Hajar2314/HawkEye-Rescue-Drone-Module/media/heatmap_0003.png

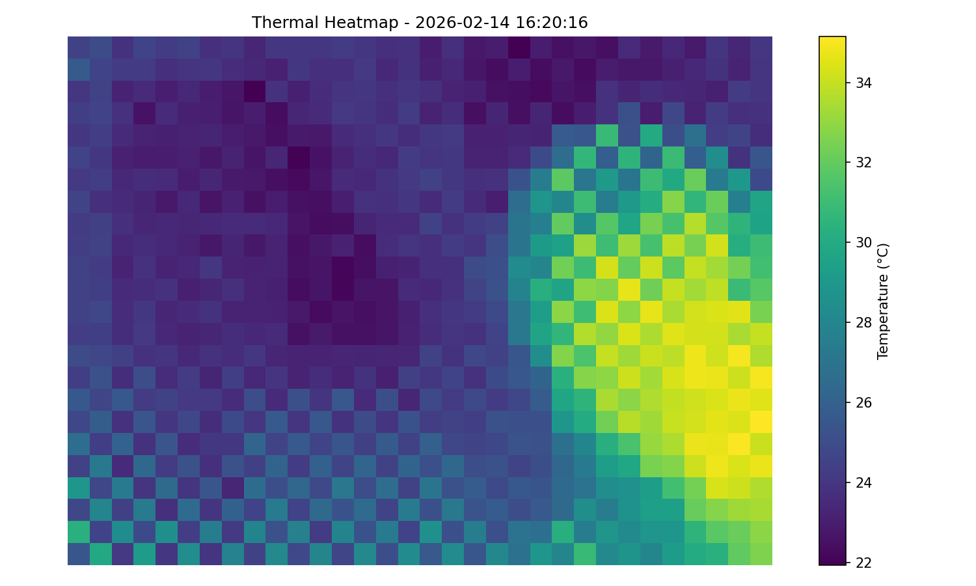
media/heatmap_0003.png
