Hajar2314/HawkEye-Rescue-Drone-Module/media/heatmap_images/heatmap_0002.png

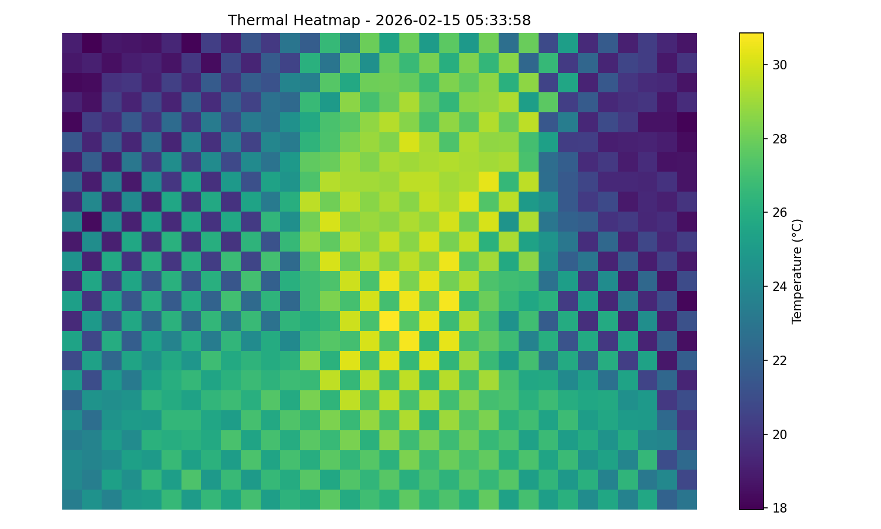
media/heatmap_images/heatmap_0002.png
