Hajar2314/HawkEye-Rescue-Drone-Module/media/heatmap_images/heatmap_0004.png

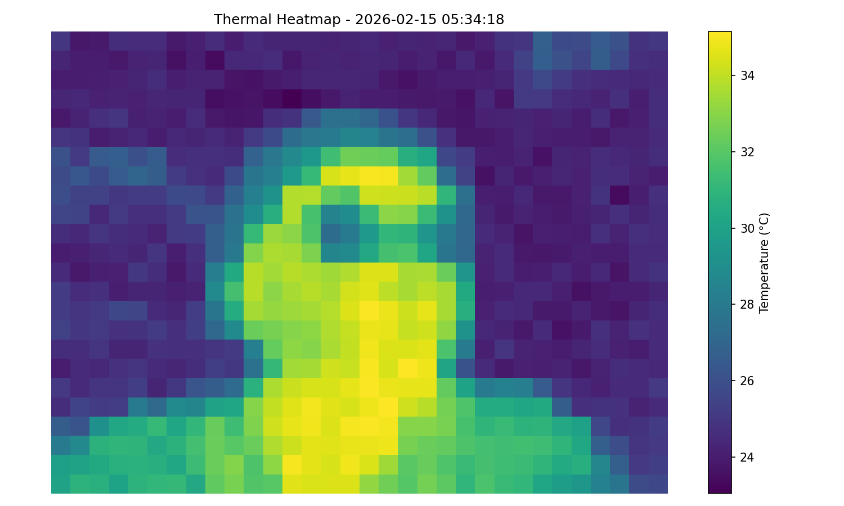
media/heatmap_images/heatmap_0004.png
