Hajar2314/HawkEye-Rescue-Drone-Module/media/heatmap_images/heatmap_0005.png

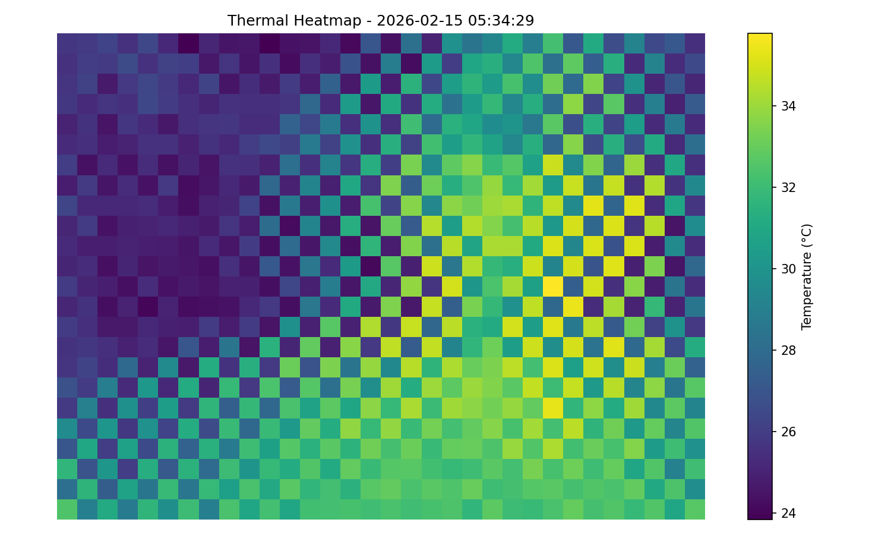
media/heatmap_images/heatmap_0005.png
