Hajar2314/HawkEye-Rescue-Drone-Module/media/photo_323210312788.jpg

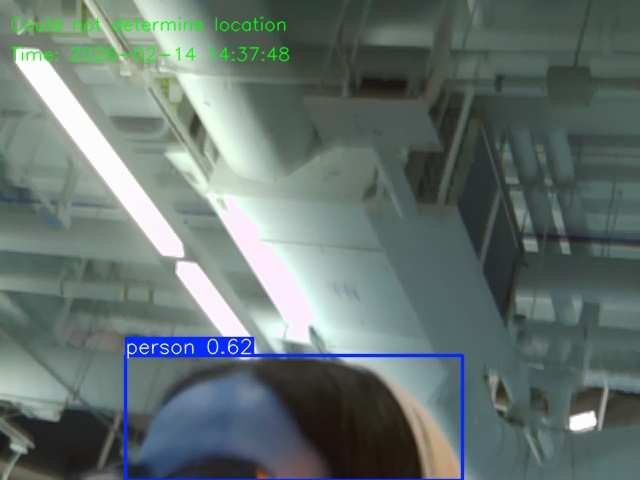
media/photo_323210312788.jpg
