Hajar2314/HawkEye-Rescue-Drone-Module/media/photo_6040880837786.jpg

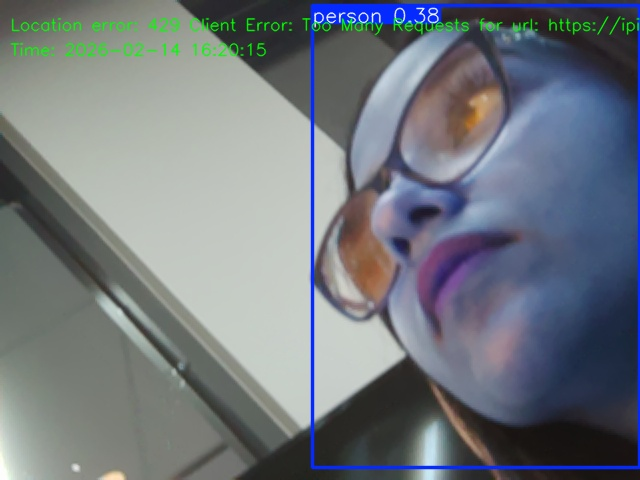
media/photo_6040880837786.jpg
