Hajar2314/HawkEye-Rescue-Drone-Module/media/Screenshot-dump/photo_65979483033.jpg

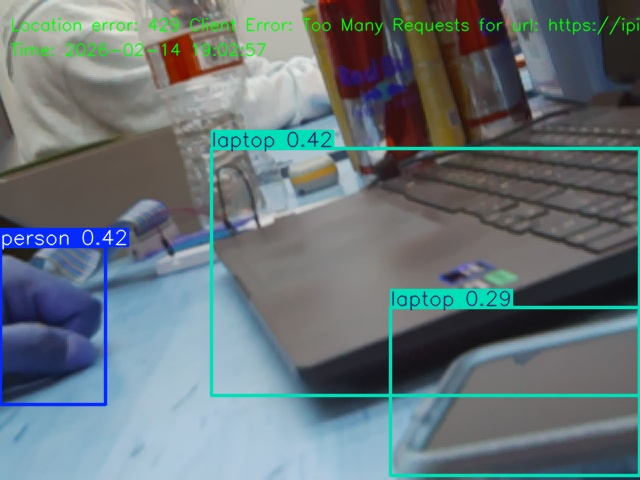
media/Screenshot-dump/photo_65979483033.jpg
