Hajar2314/HawkEye-Rescue-Drone-Module/media/Screenshot-dump/photo_150695907242.jpg

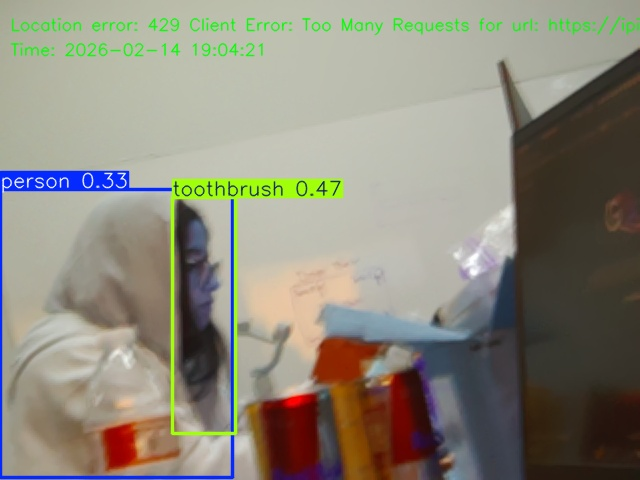
media/Screenshot-dump/photo_150695907242.jpg
