Hajar2314/HawkEye-Rescue-Drone-Module/media/Screenshot-dump/photo_160943007310.jpg

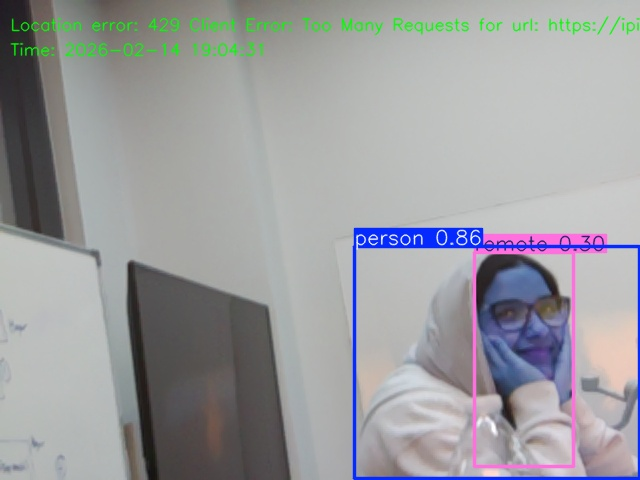
media/Screenshot-dump/photo_160943007310.jpg
