Hajar2314/HawkEye-Rescue-Drone-Module/media/Screenshot-dump/photo_250089213979.jpg

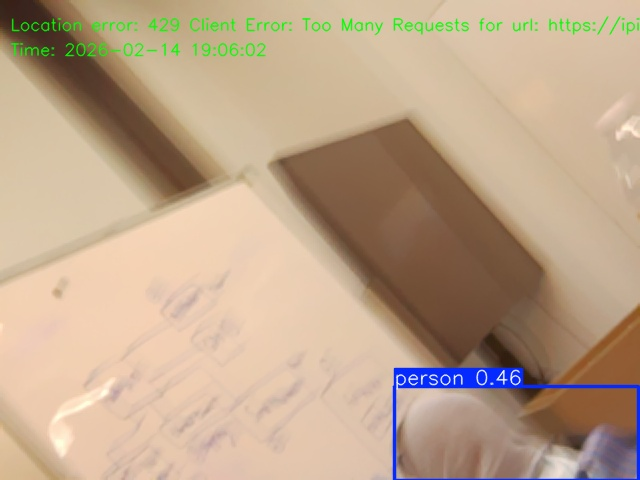
media/Screenshot-dump/photo_250089213979.jpg
