Hajar2314/HawkEye-Rescue-Drone-Module/media/Screenshot-dump/photo_260206468602.jpg

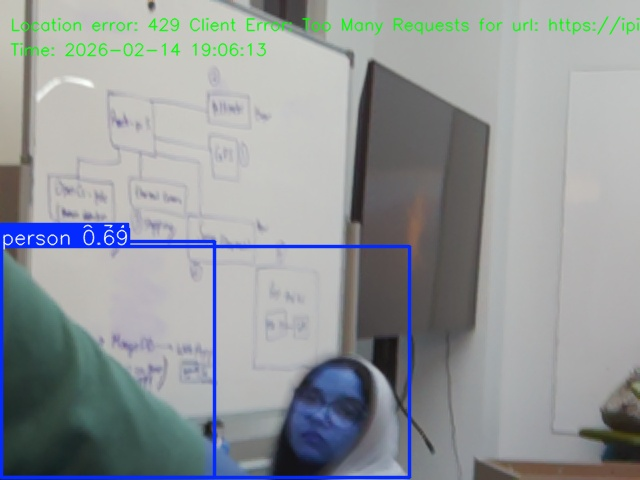
media/Screenshot-dump/photo_260206468602.jpg
