Hajar2314/HawkEye-Rescue-Drone-Module/media/Screenshot-dump/photo_1018532582539.jpg

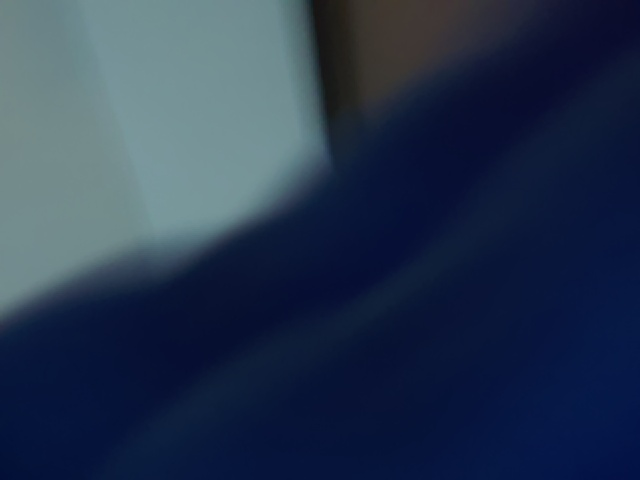
media/Screenshot-dump/photo_1018532582539.jpg
