Hajar2314/HawkEye-Rescue-Drone-Module/media/Screenshot-dump/photo_1371170427736.jpg

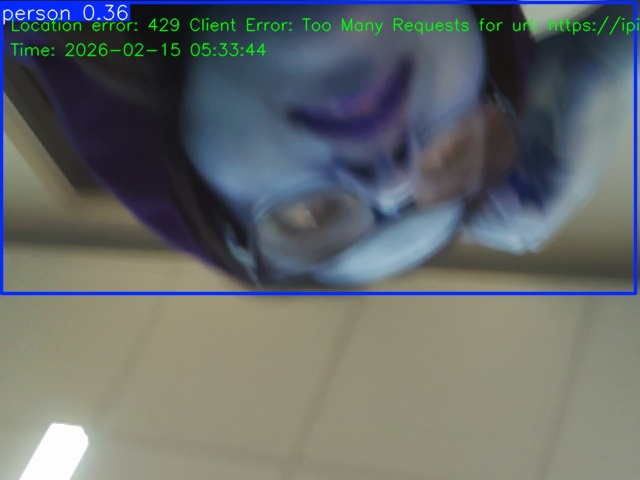
media/Screenshot-dump/photo_1371170427736.jpg
