Hajar2314/HawkEye-Rescue-Drone-Module/media/Screenshot-dump/photo_1381337316249.jpg

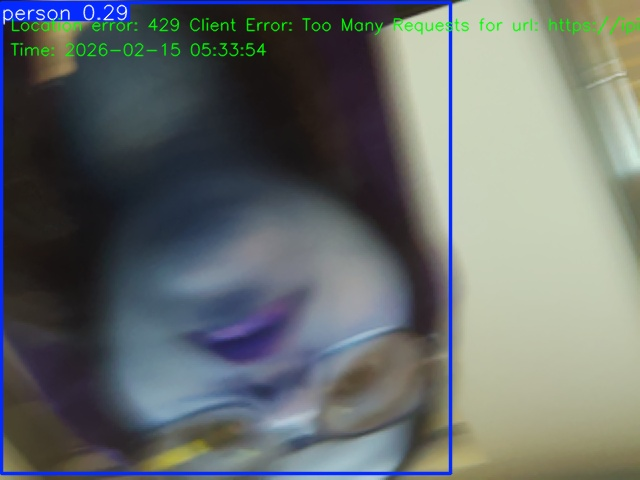
media/Screenshot-dump/photo_1381337316249.jpg
