Hajar2314/HawkEye-Rescue-Drone-Module/media/Screenshot-dump/photo_1391352862336.jpg

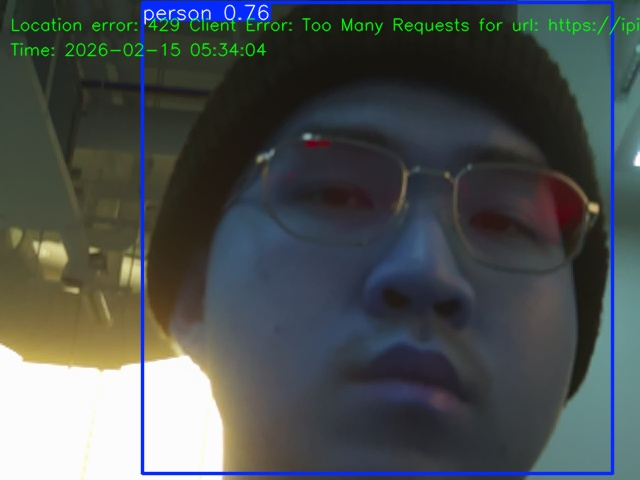
media/Screenshot-dump/photo_1391352862336.jpg
