Hajar2314/HawkEye-Rescue-Drone-Module/media/Screenshot-dump/photo_1401934641922.jpg

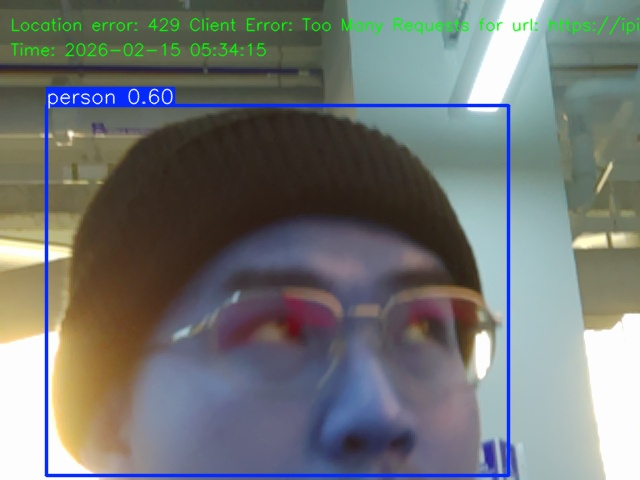
media/Screenshot-dump/photo_1401934641922.jpg
