Hajar2314/HawkEye-Rescue-Drone-Module/media/Screenshot-dump/photo_1423939126094.jpg

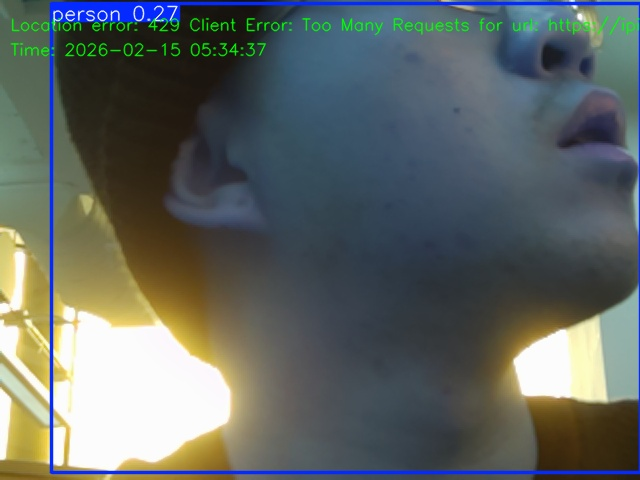
media/Screenshot-dump/photo_1423939126094.jpg
