Hajar2314/HawkEye-Rescue-Drone-Module/media/Screenshot-dump/photo_1434042093514.jpg

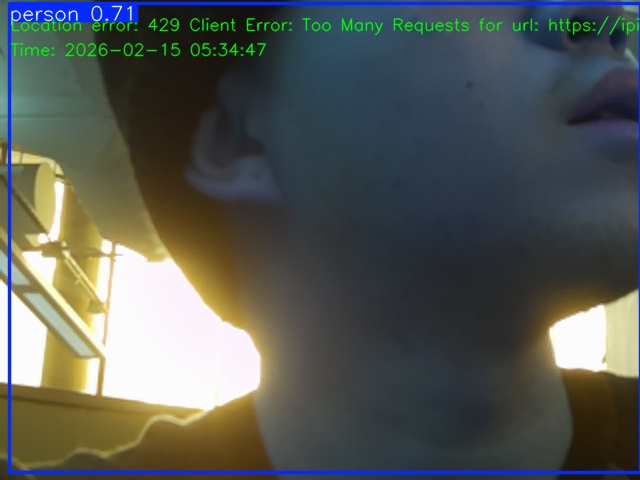
media/Screenshot-dump/photo_1434042093514.jpg
