Hajar2314/HawkEye-Rescue-Drone-Module/media/Screenshot-dump/photo_14077549384607.jpg

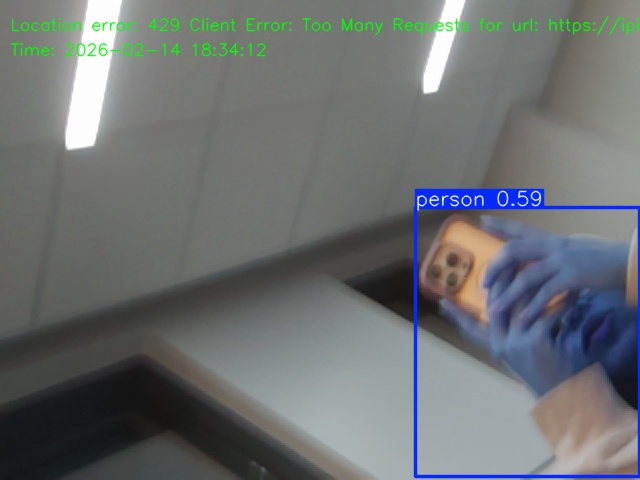
media/Screenshot-dump/photo_14077549384607.jpg
