Hajar2314/HawkEye-Rescue-Drone-Module/media/Screenshot-dump/photo_14099003779039.jpg

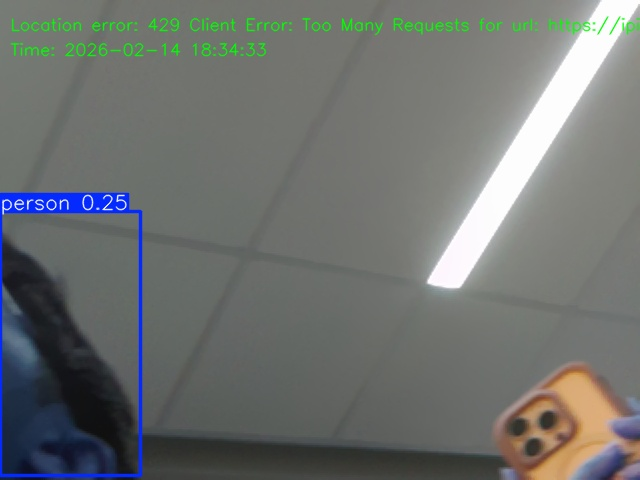
media/Screenshot-dump/photo_14099003779039.jpg
