Hajar2314/HawkEye-Rescue-Drone-Module/media/Screenshot-dump/photo_14109056814681.jpg

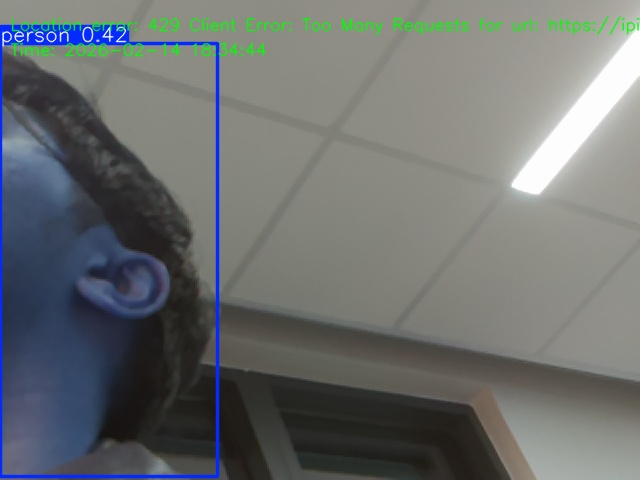
media/Screenshot-dump/photo_14109056814681.jpg
