Hajar2314/HawkEye-Rescue-Drone-Module/media/Screenshot-dump/photo_14119194947916.jpg

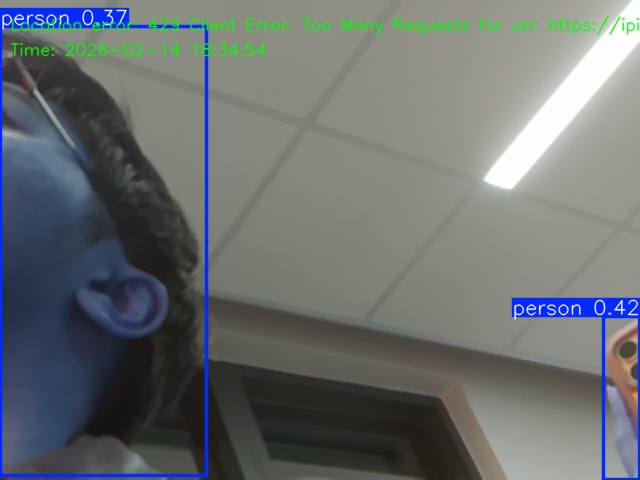
media/Screenshot-dump/photo_14119194947916.jpg
