Hajar2314/HawkEye-Rescue-Drone-Module/media/Screenshot-dump/photo_14129324060317.jpg

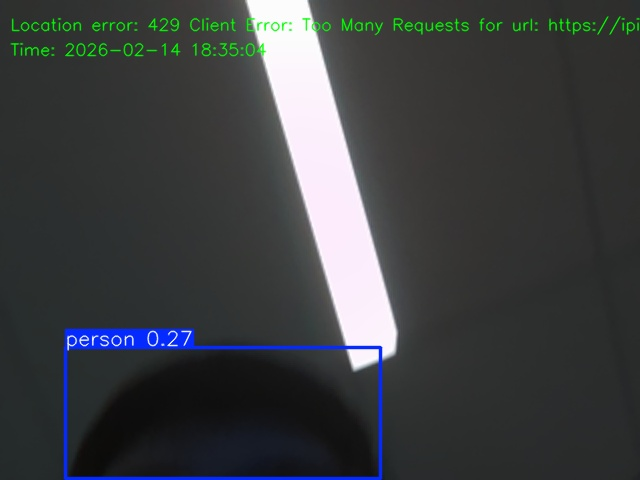
media/Screenshot-dump/photo_14129324060317.jpg
