Hajar2314/HawkEye-Rescue-Drone-Module/media/Screenshot-dump/photo_14321042564462.jpg

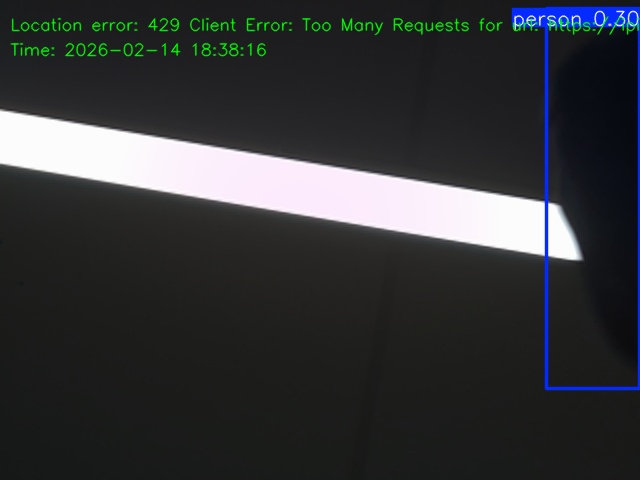
media/Screenshot-dump/photo_14321042564462.jpg
