Hajar2314/HawkEye-Rescue-Drone-Module/media/Screenshot-dump/photo_14332644091011.jpg

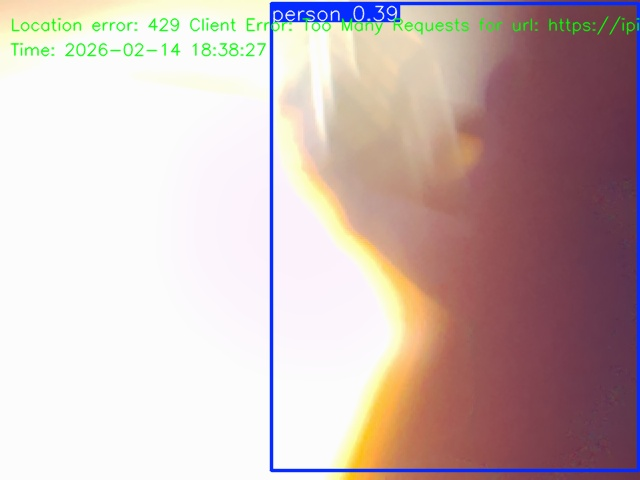
media/Screenshot-dump/photo_14332644091011.jpg
